analoghifi/Thel-SAC-30.2-30.3/docs/original german (not corrected)/Freq_Tab_2016.png

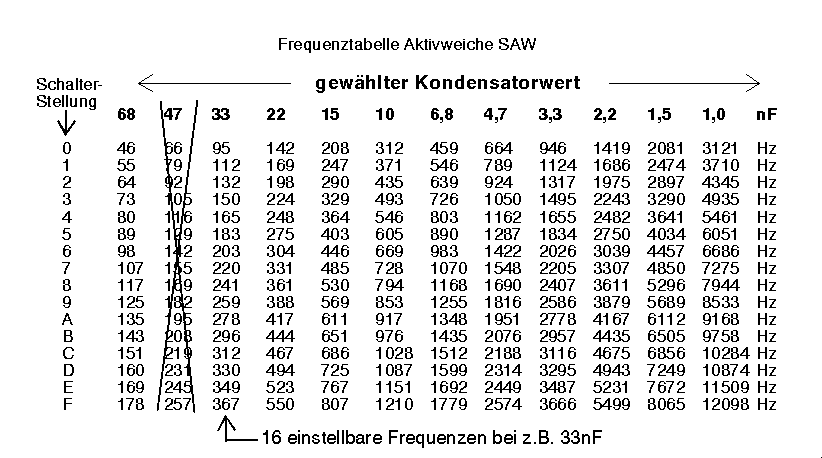
docs/original german (not corrected)/Freq_Tab_2016.png
