analoghifi/Thel-SAC-30.2-30.3/docs/original german (not corrected)/SAW-D2.GIF

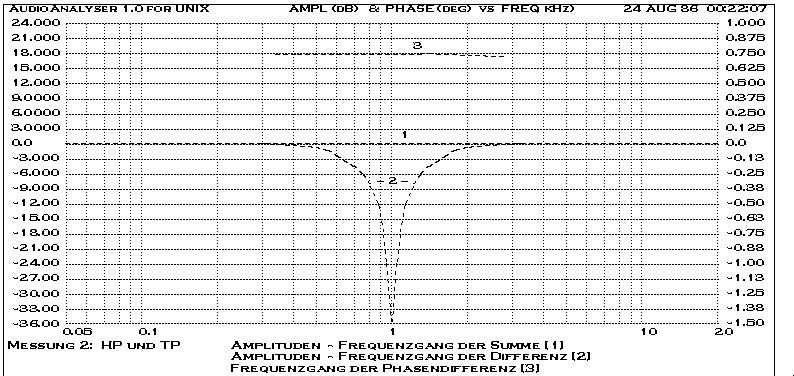
docs/original german (not corrected)/SAW-D2.GIF
