analoghifi/Thel-SAC-30.2-30.3/docs/original german (not corrected)/SAW-D3.GIF

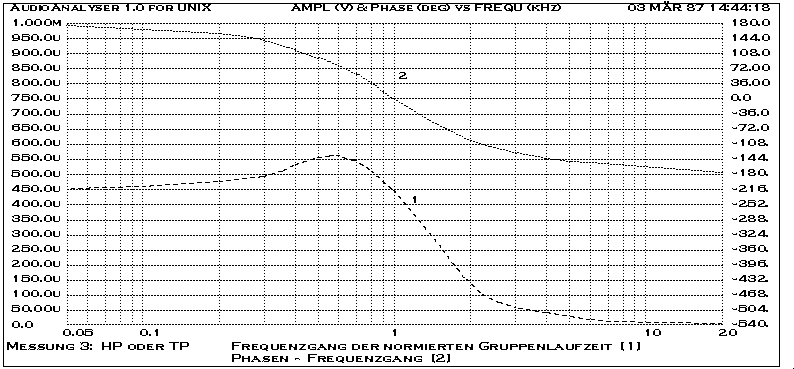
docs/original german (not corrected)/SAW-D3.GIF
