analoghifi/Thel-SAC-30.2-30.3/docs/original german (not corrected)/SawEing.jpg

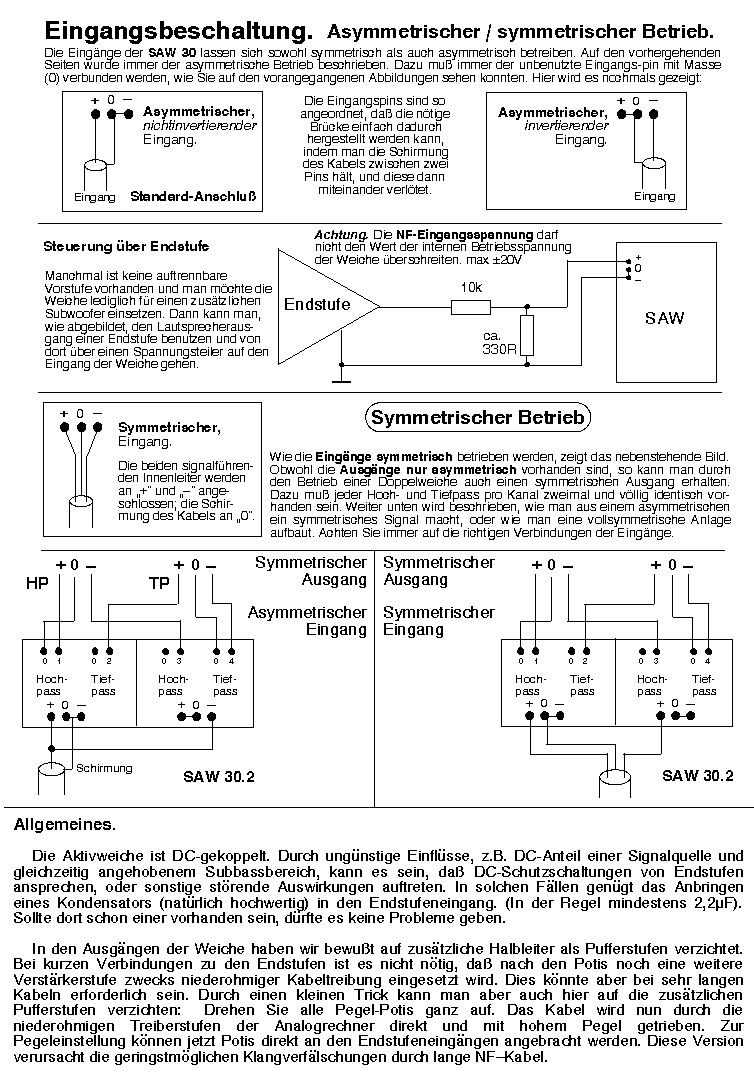
docs/original german (not corrected)/SawEing.jpg
