analoghifi/Thel-SAC-30.2-30.3/hardware/2) version 07.2017 until now/KiCad/original/SAW30_original_1Layer_THT__bottom.png

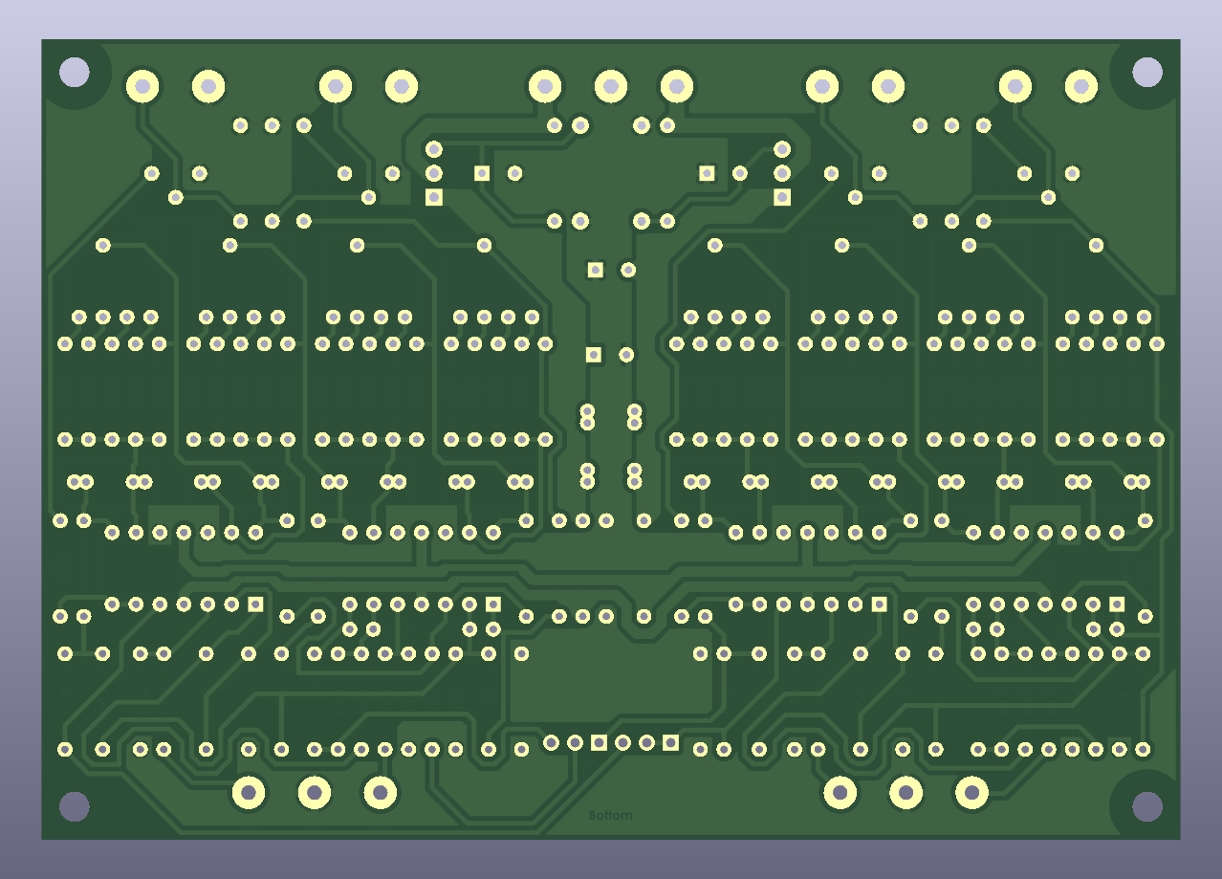
hardware/2) version 07.2017 until now/KiCad/original/SAW30_original_1Layer_THT__bottom.png
