analoghifi/Thel-SAC-30.2-30.3/hardware/2) version 07.2017 until now/PCB_original_SAW-30.jpg

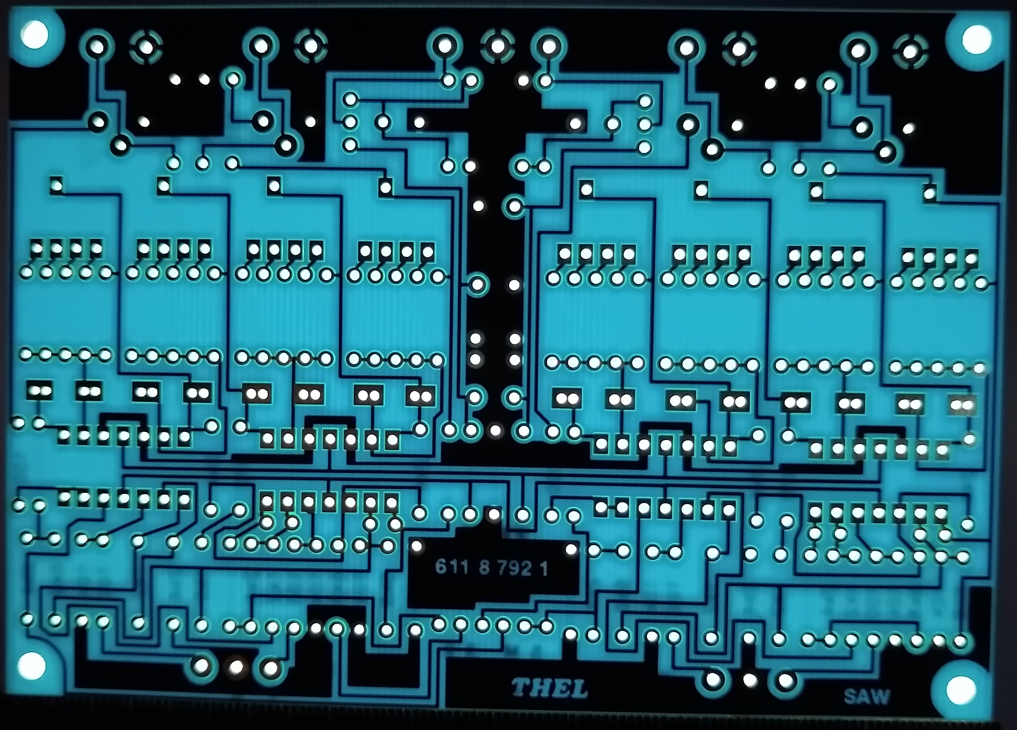
hardware/2) version 07.2017 until now/PCB_original_SAW-30.jpg
