analoghifi/Thel-SAC-30.2-30.3/hardware/3) version 2011-2017/DSC04987.jpg

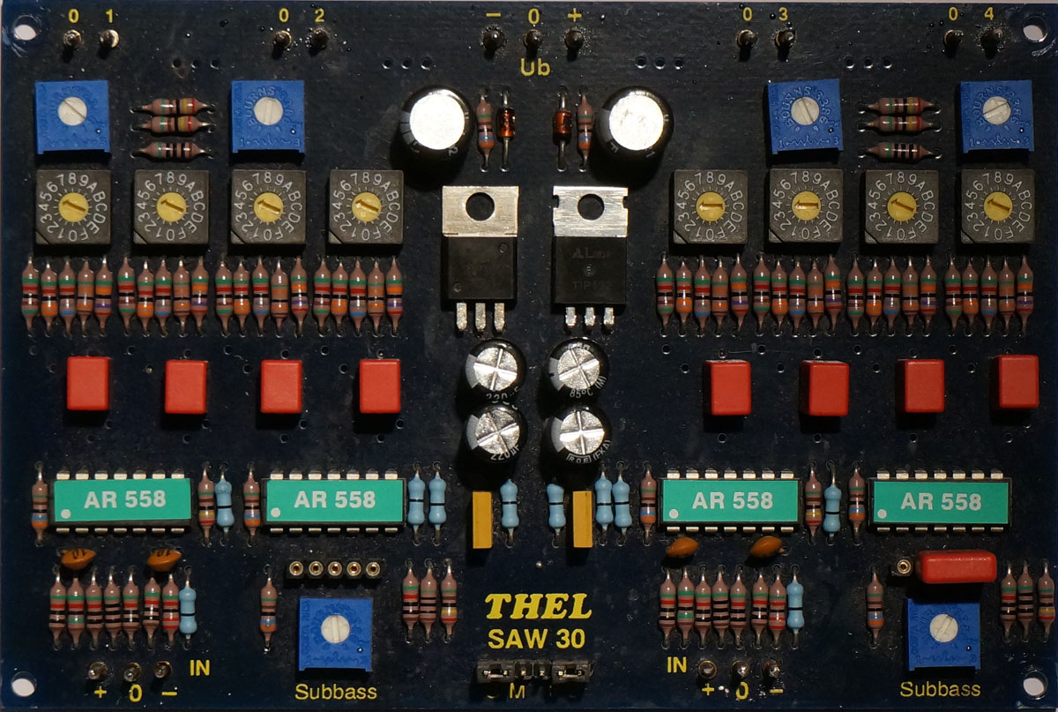
hardware/3) version 2011-2017/DSC04987.jpg
