analoghifi/Thel-SAC-30.2-30.3/hardware/3) version 2011-2017/KiCad/original/SAW30_v2011-2017_original1Layer_THT__3D_with_trimpots.jpg

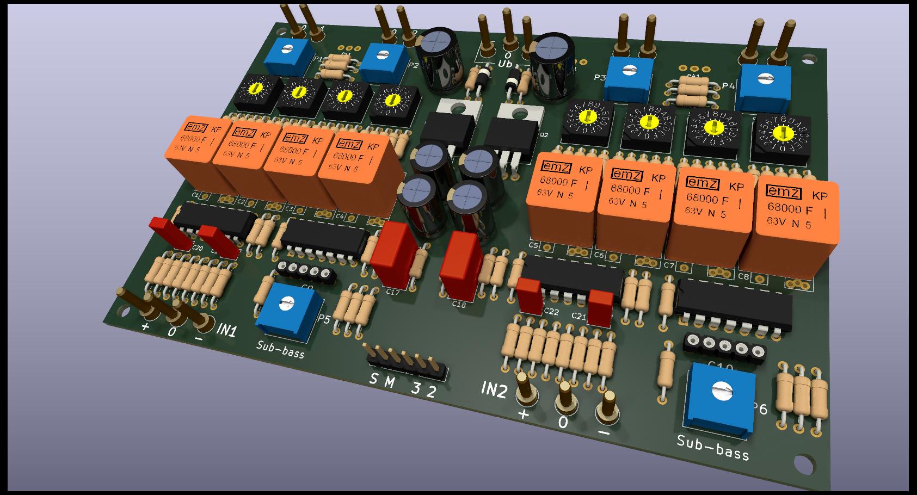
hardware/3) version 2011-2017/KiCad/original/SAW30_v2011-2017_original1Layer_THT__3D_with_trimpots.jpg
