analoghifi/Thel-SAC-30.2-30.3/hardware/3) version 2011-2017/SAW-30_2011_2017_bottom.jpg

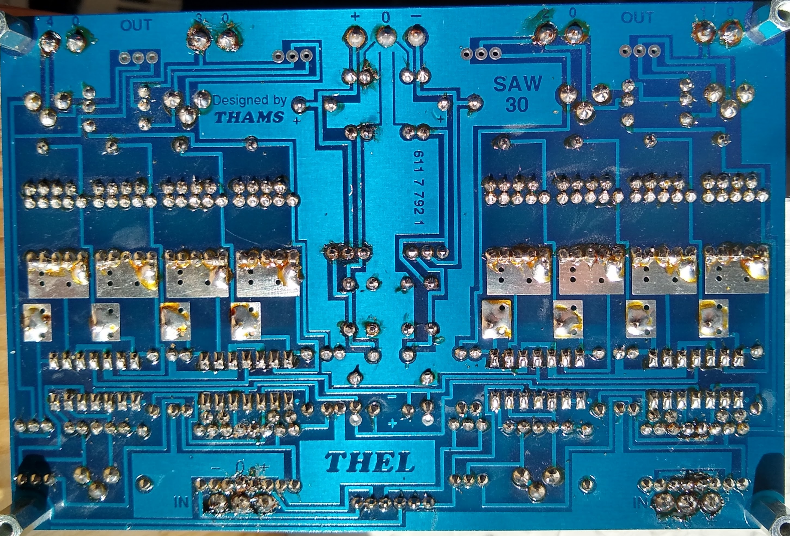
hardware/3) version 2011-2017/SAW-30_2011_2017_bottom.jpg
