analoghifi/Thel-SAC-30.2-30.3/hardware/4) version 2005 - 3.2011/saw30_2.jpg

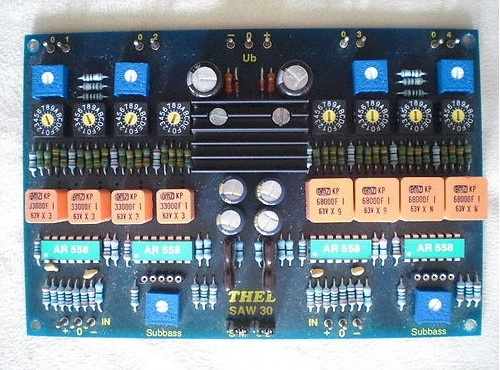
hardware/4) version 2005 - 3.2011/saw30_2.jpg
