analoghifi/Thel-SAC-30.2-30.3/hardware/4) version 2005 - 3.2011/SAW30_2005 - 03.2011.jpg

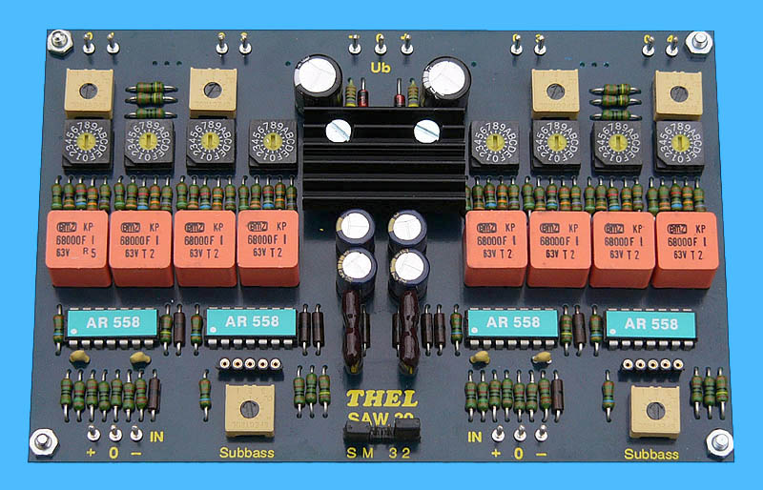
hardware/4) version 2005 - 3.2011/SAW30_2005 - 03.2011.jpg
