analoghifi/Thel-SAC-30.2-30.3/hardware/5) version 1995-2005/2saw30_1.jpg

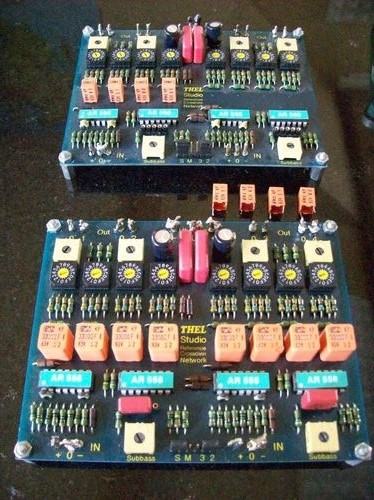
hardware/5) version 1995-2005/2saw30_1.jpg
