analoghifi/Thel-SAC-30.2-30.3/hardware/5) version 1995-2005/saw_1995-2005.jpg

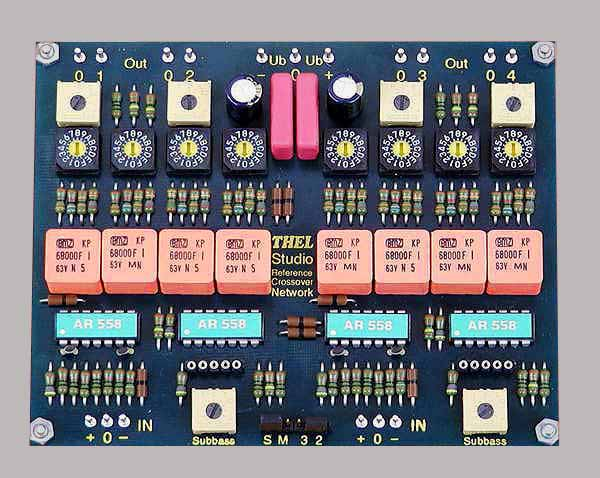
hardware/5) version 1995-2005/saw_1995-2005.jpg
