analoghifi/Thel-SAC-30.2-30.3/hardware/5) version 1995-2005/Thel-Audio-SAW-30-analoge-Referenz-Aktivweiche-vollsymmetrischer-dualmono.jpg

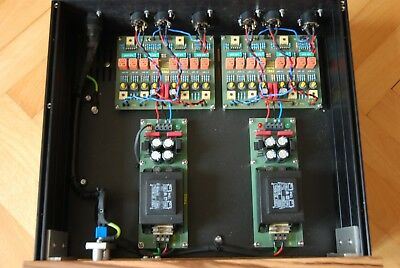
hardware/5) version 1995-2005/Thel-Audio-SAW-30-analoge-Referenz-Aktivweiche-vollsymmetrischer-dualmono.jpg
