analoghifi/Thel-SAC-30.2-30.3/hardware/6) version 1991-1994/SAW_1991-1994.jpg

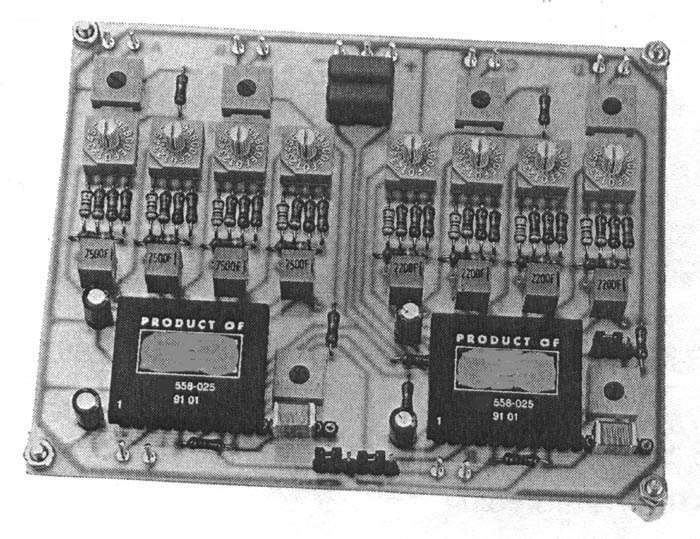
hardware/6) version 1991-1994/SAW_1991-1994.jpg
