analoghifi/Thel-SAC-30.2-30.3/hardware/6) version 1991-1994/Thel_SAW_30_1991-1994__2.jpg

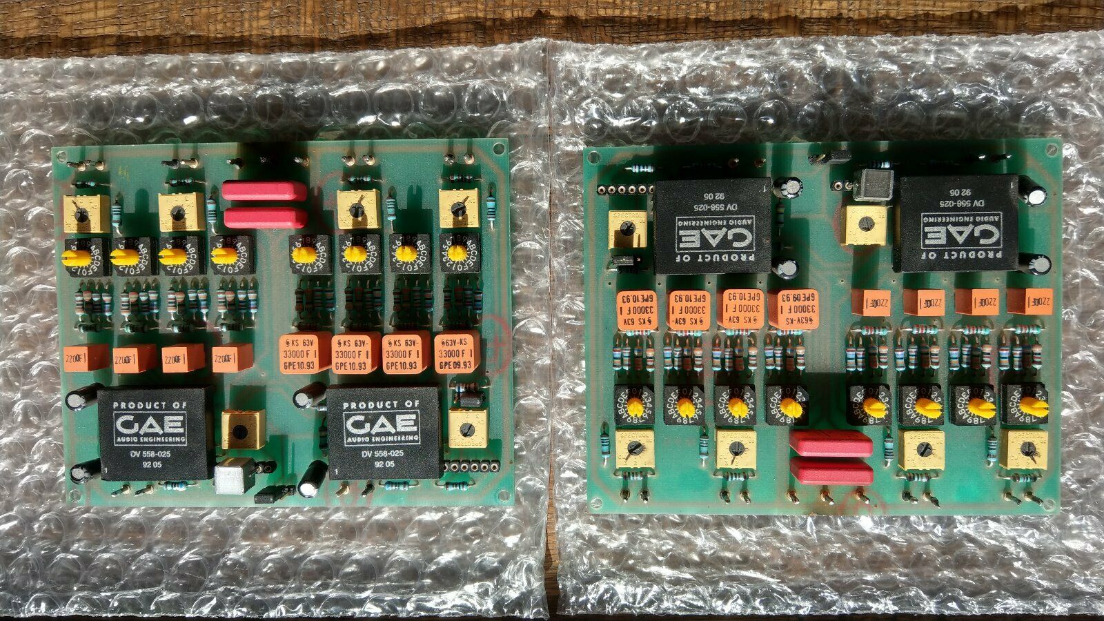
hardware/6) version 1991-1994/Thel_SAW_30_1991-1994__2.jpg
