analoghifi/Thel-SAC-30.2-30.3/docs/components datasheets/Onsemi_MC33079P.jpg

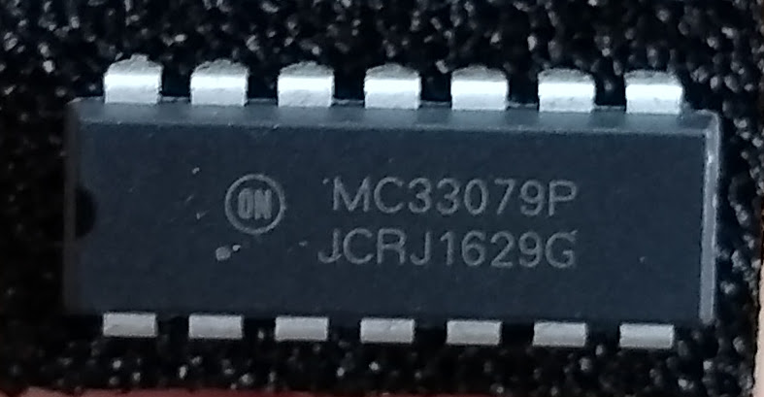
docs/components datasheets/Onsemi_MC33079P.jpg
